goakley/TokiPonaKeyboard/docs/joysticks.webp

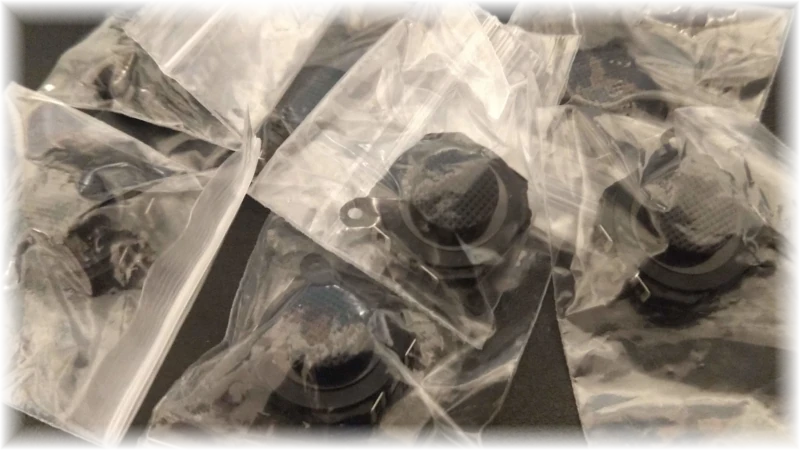
docs/joysticks.webp
