goakley/TokiPonaKeyboard/docs/pcb.webp

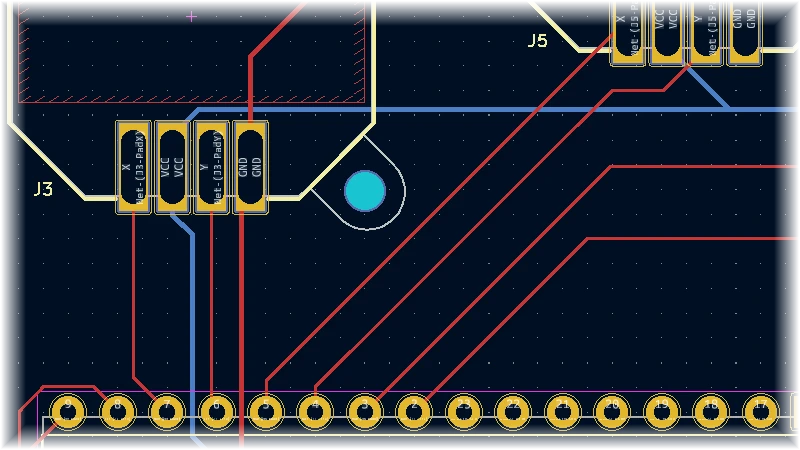
docs/pcb.webp
